VIPQualityPost/polarizer-illuminator/firmware/src/adc.cpp

#include <Arduino.h>
#include "RTTStream.h"
#include "adc.h"

ADC_HandleTypeDef hadc1;
DMA_HandleTypeDef hdma_adc1;

extern RTTStream rtt;

void init_adc(void)
{
  ADC_MultiModeTypeDef multimode = {0};
  ADC_ChannelConfTypeDef sConfig = {0};

  hadc1.Instance = ADC1;
  hadc1.Init.ClockPrescaler = ADC_CLOCK_ASYNC_DIV16;
  hadc1.Init.Resolution = ADC_RESOLUTION_12B;
  hadc1.Init.DataAlign = ADC_DATAALIGN_RIGHT;
  hadc1.Init.GainCompensation = 0;
  hadc1.Init.ScanConvMode = ADC_SCAN_ENABLE;
  hadc1.Init.EOCSelection = ADC_EOC_SINGLE_CONV;
  hadc1.Init.LowPowerAutoWait = DISABLE;
  hadc1.Init.ContinuousConvMode = ENABLE;
  hadc1.Init.NbrOfConversion = 2;
  hadc1.Init.DiscontinuousConvMode = DISABLE;
  hadc1.Init.ExternalTrigConv = ADC_SOFTWARE_START;
  hadc1.Init.ExternalTrigConvEdge = ADC_EXTERNALTRIGCONVEDGE_NONE;
  // hadc1.Init.ExternalTrigConv = ADC_EXTERNALTRIG_T2_TRGO;
  // hadc1.Init.ExternalTrigConvEdge = ADC_EXTERNALTRIGCONVEDGE_RISING;
  hadc1.Init.DMAContinuousRequests = ENABLE;
  hadc1.Init.Overrun = ADC_OVR_DATA_PRESERVED;
  hadc1.Init.OversamplingMode = DISABLE;
  if (HAL_ADC_Init(&hadc1) != HAL_OK)
  {
    rtt.println("Issue initializing ADC.");
  }

  multimode.Mode = ADC_MODE_INDEPENDENT;
  if (HAL_ADCEx_MultiModeConfigChannel(&hadc1, &multimode) != HAL_OK)
  {
    rtt.println("Issue configuring ADC multimode.");
  }

  // Left potentiometer
  sConfig.Channel = ADC_CHANNEL_1;
  sConfig.Rank = ADC_REGULAR_RANK_1;
  sConfig.SamplingTime = ADC_SAMPLETIME_2CYCLES_5;
  sConfig.SingleDiff = ADC_SINGLE_ENDED;
  sConfig.OffsetNumber = ADC_OFFSET_NONE;
  sConfig.Offset = 0;
  if (HAL_ADC_ConfigChannel(&hadc1, &sConfig) != HAL_OK)
  {
    rtt.println("Issue configuring ADC1 IN1.");
  }

  // Right potentiometer
  sConfig.Channel = ADC_CHANNEL_2;
  sConfig.Rank = ADC_REGULAR_RANK_2;

  if(HAL_ADC_ConfigChannel(&hadc1, &sConfig) != HAL_OK)
  {
    rtt.println("Issue configuring ADC1 IN2.");
  }

  HAL_ADCEx_Calibration_Start(&hadc1, ADC_SINGLE_ENDED);
}

void gpio_config_adc(ADC_HandleTypeDef* adcHandle)
{

  GPIO_InitTypeDef GPIO_InitStruct = {0};
  RCC_PeriphCLKInitTypeDef PeriphClkInit = {0};

  PeriphClkInit.PeriphClockSelection = RCC_PERIPHCLK_ADC12;
  PeriphClkInit.Adc12ClockSelection = RCC_ADC12CLKSOURCE_SYSCLK;

  if (HAL_RCCEx_PeriphCLKConfig(&PeriphClkInit) != HAL_OK)
  {
    rtt.println("ADC DMA Clock configuration failed.");
  }

  __HAL_RCC_ADC12_CLK_ENABLE();
  __HAL_RCC_GPIOA_CLK_ENABLE();
  /**ADC1 GPIO Configuration
  PA0     ------> ADC1_IN1
  PA1     ------> ADC1_IN2
  */
  GPIO_InitStruct.Pin = GPIO_PIN_0|GPIO_PIN_1;
  GPIO_InitStruct.Mode = GPIO_MODE_ANALOG;
  GPIO_InitStruct.Pull = GPIO_NOPULL;
  HAL_GPIO_Init(GPIOA, &GPIO_InitStruct);

  hdma_adc1.Instance = DMA1_Channel3;
  hdma_adc1.Init.Request = DMA_REQUEST_ADC1;
  hdma_adc1.Init.Direction = DMA_PERIPH_TO_MEMORY;
  hdma_adc1.Init.PeriphInc = DMA_PINC_DISABLE;
  hdma_adc1.Init.MemInc = DMA_MINC_ENABLE;
  hdma_adc1.Init.PeriphDataAlignment = DMA_PDATAALIGN_HALFWORD;
  hdma_adc1.Init.MemDataAlignment = DMA_MDATAALIGN_HALFWORD;
  hdma_adc1.Init.Mode = DMA_CIRCULAR;
  hdma_adc1.Init.Priority = DMA_PRIORITY_LOW;
  
  if (HAL_DMA_Init(&hdma_adc1) != HAL_OK)
  {
    rtt.println("ADC DMA initialization failed.");
  }

  __HAL_LINKDMA(adcHandle,DMA_Handle,hdma_adc1);

  // HAL_NVIC_SetPriority(ADC1_2_IRQn, 0, 0);
  // HAL_NVIC_EnableIRQ(ADC1_2_IRQn);
}
