VIPQualityPost/polarizer-illuminator/firmware/src/dma.cpp

#include "dma.h"

void init_dma(void)
{
  HAL_NVIC_SetPriority(DMA1_Channel3_IRQn, 0, 0);
  HAL_NVIC_EnableIRQ(DMA1_Channel3_IRQn);
}

extern "C" {
void DMA1_Channel3_IRQHandler(void)
{
  HAL_DMA_IRQHandler(&hdma_adc1);
}
}
