VIPQualityPost/polarizer-illuminator/firmware/src/opa.cpp

#include <Arduino.h>
#include "RTTStream.h"
#include "opa.h"

OPAMP_HandleTypeDef hopamp1;

extern RTTStream rtt;

void init_opa(void)
{
  hopamp1.Instance = OPAMP1;
  hopamp1.Init.PowerMode = OPAMP_POWERMODE_NORMAL;
  hopamp1.Init.Mode = OPAMP_FOLLOWER_MODE;
  hopamp1.Init.NonInvertingInput = OPAMP_NONINVERTINGINPUT_DAC;
  hopamp1.Init.InternalOutput = DISABLE;
  hopamp1.Init.TimerControlledMuxmode = OPAMP_TIMERCONTROLLEDMUXMODE_DISABLE;
  hopamp1.Init.UserTrimming = OPAMP_TRIMMING_FACTORY;
  
  if(HAL_OPAMP_Init(&hopamp1) != HAL_OK){
    rtt.println("Issue initalizing OPAMP.");
  }

  HAL_OPAMP_SelfCalibrate(&hopamp1);
}

void gpio_config_opa(OPAMP_HandleTypeDef* opampHandle)
{

  GPIO_InitTypeDef GPIO_InitStruct = {0};
  if(opampHandle->Instance==OPAMP1)
  {
    __HAL_RCC_GPIOA_CLK_ENABLE();
    /**OPAMP1 GPIO Configuration
    PA2     ------> OPAMP1_VOUT
    */
    GPIO_InitStruct.Pin = GPIO_PIN_2;
    GPIO_InitStruct.Mode = GPIO_MODE_ANALOG;
    GPIO_InitStruct.Pull = GPIO_NOPULL;
    HAL_GPIO_Init(GPIOA, &GPIO_InitStruct);
  }
}
